WilliamAlexanda/Open_Bio-Skin/Hardware/PCB/Little board/1.jpg

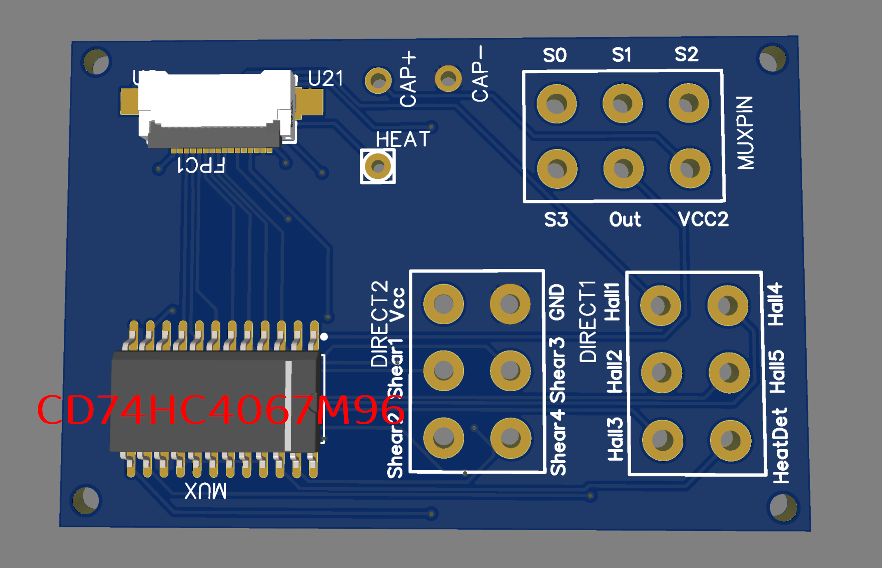
Hardware/PCB/Little board/1.jpg
